Newaysfactory/vespa-remote/electronics/KiCAD/Drawings/rev1/3DVespaRemoteControl-RedBack.png

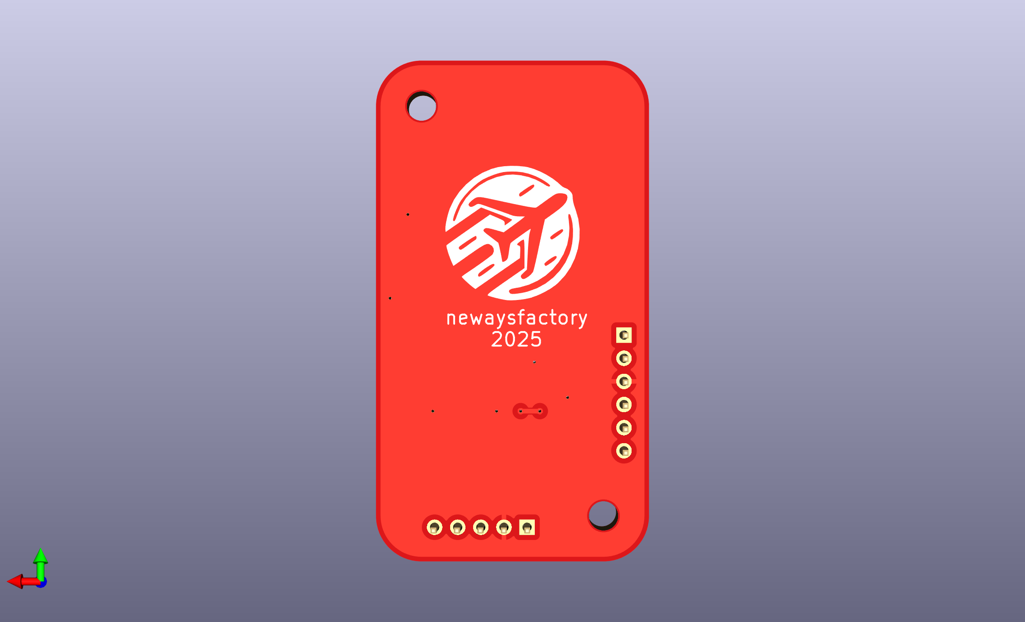
electronics/KiCAD/Drawings/rev1/3DVespaRemoteControl-RedBack.png
