Newaysfactory/vespa-remote/electronics/KiCAD/Drawings/rev1/3DVespaRemoteControl-RedFront30deg.png

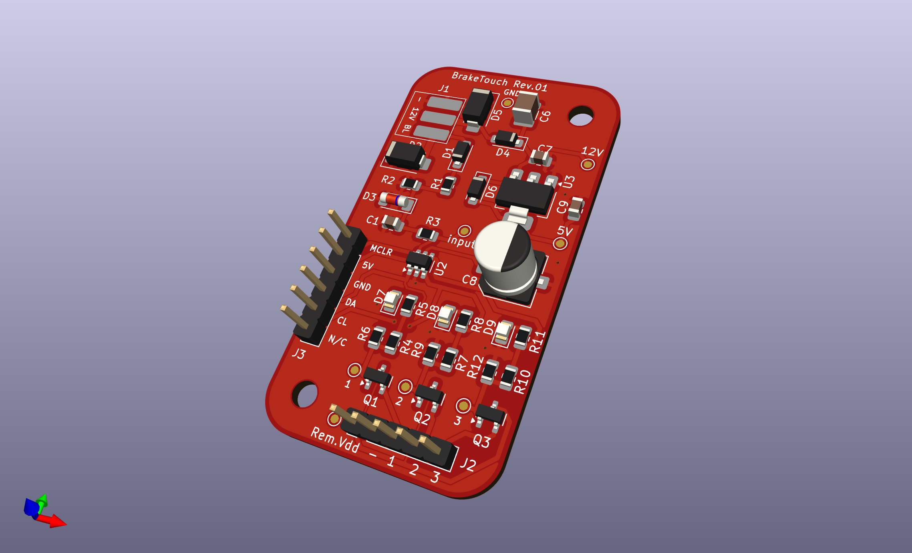
electronics/KiCAD/Drawings/rev1/3DVespaRemoteControl-RedFront30deg.png
