Newaysfactory/vespa-remote/Schema_PX_Euro3.jpeg.25685b8193745e915f18c49f5028302e.jpeg

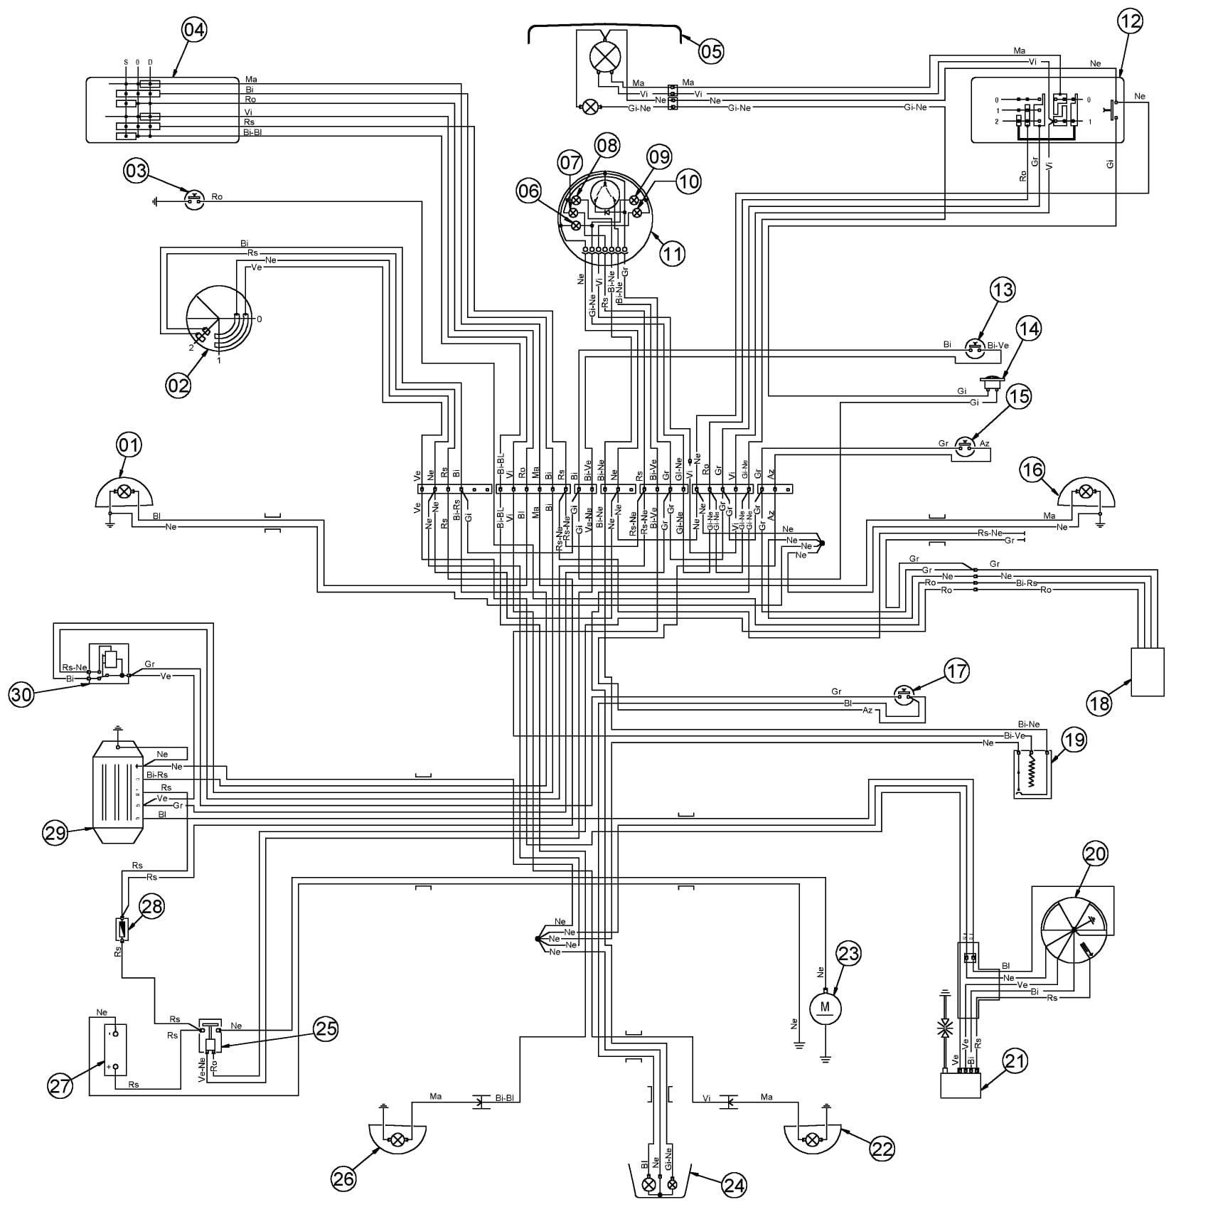
Schema_PX_Euro3.jpeg.25685b8193745e915f18c49f5028302e.jpeg
