Newaysfactory/vespa-remote/electronics/KiCAD/Print Schematic.png

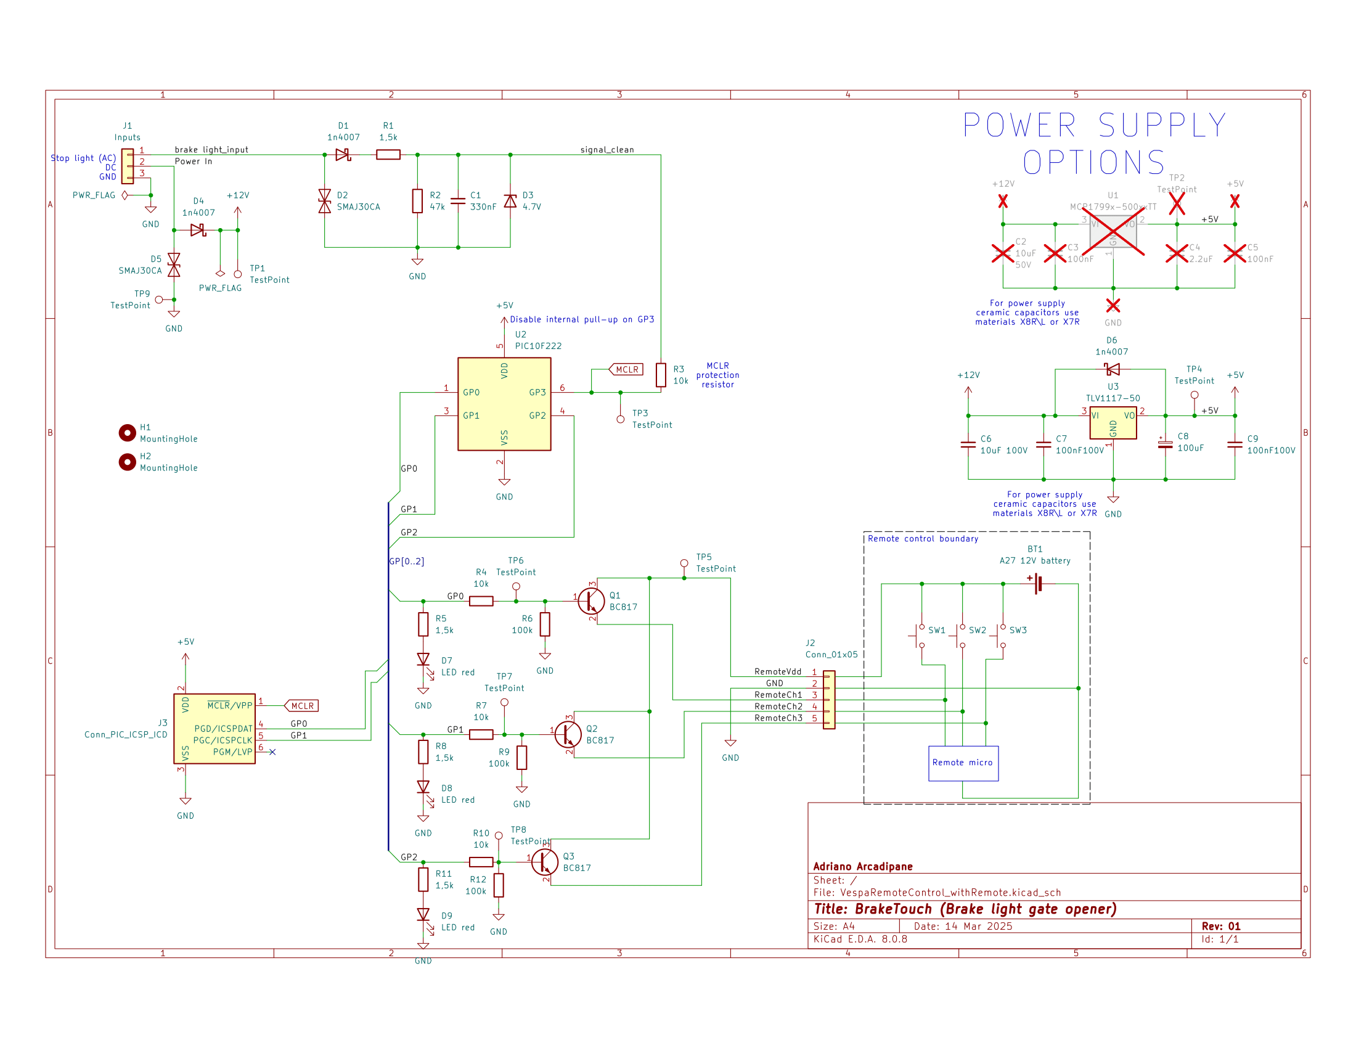
electronics/KiCAD/Print Schematic.png
